emilyanthony4244/Sheikah_Slate/Assets/FB_IMG_1660274705326.jpg

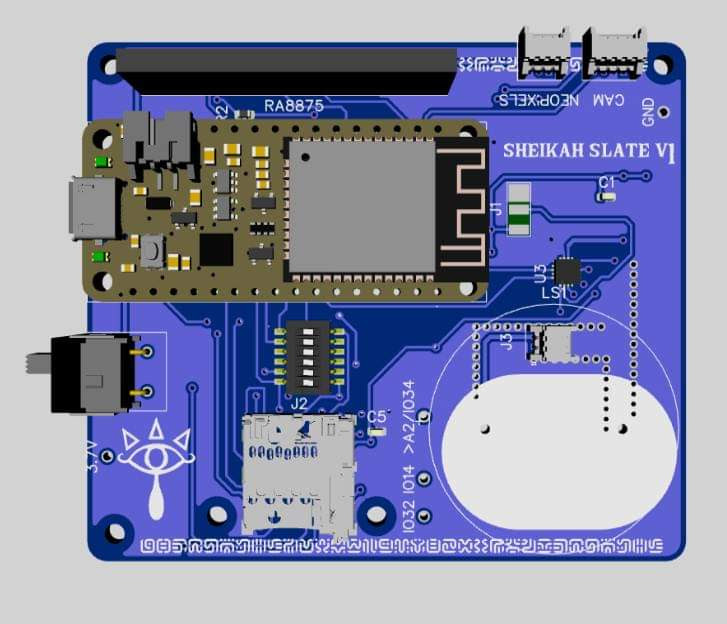
Assets/FB_IMG_1660274705326.jpg
