emilyanthony4244/Sheikah_Slate/Main Control Board/Bottom Copper.PNG

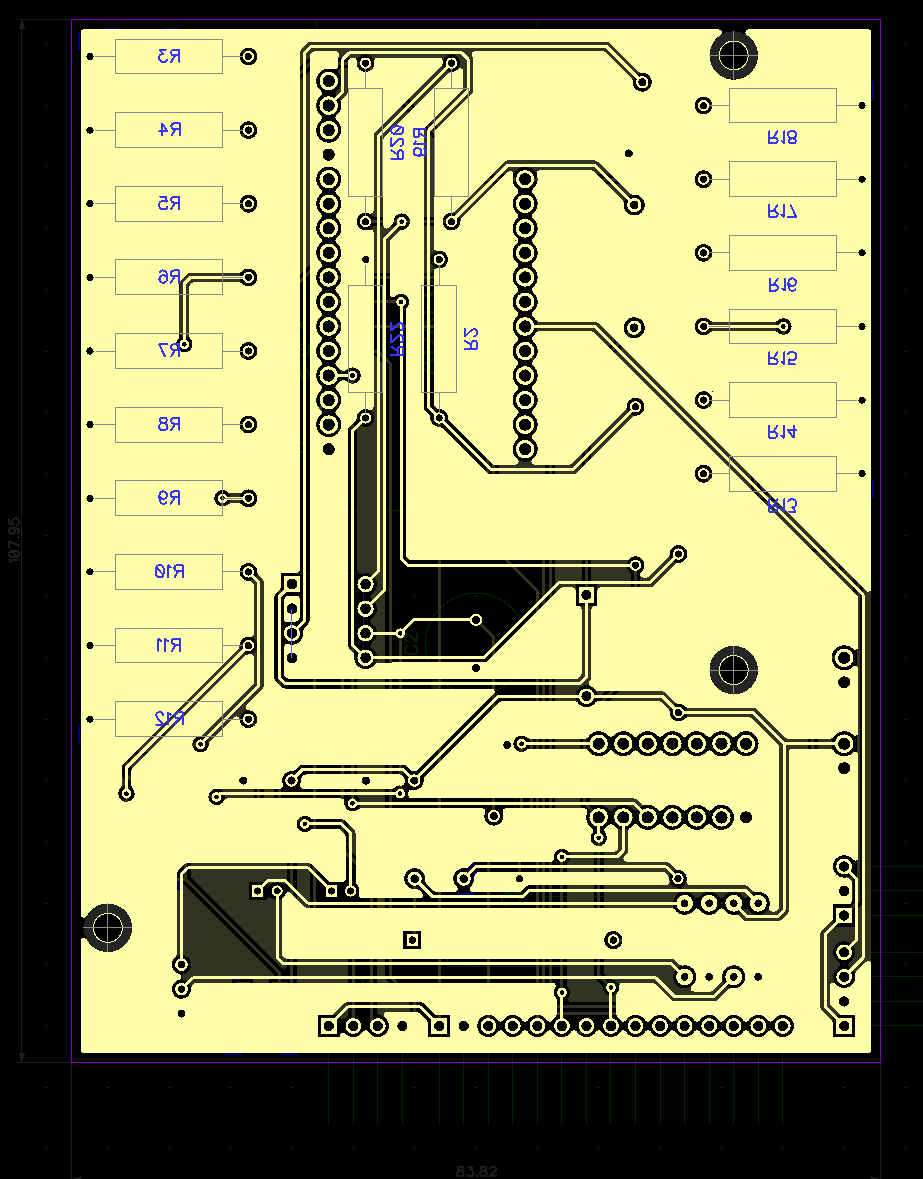
Main Control Board/Bottom Copper.PNG
