emilyanthony4244/Sheikah_Slate/Main Control Board/bottom.PNG

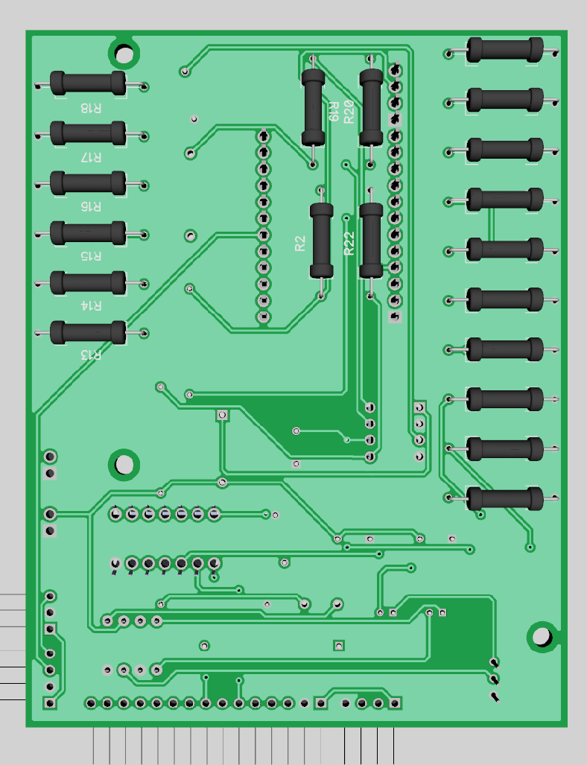
Main Control Board/bottom.PNG
