emilyanthony4244/Sheikah_Slate/Main Control Board/Top Copper.PNG

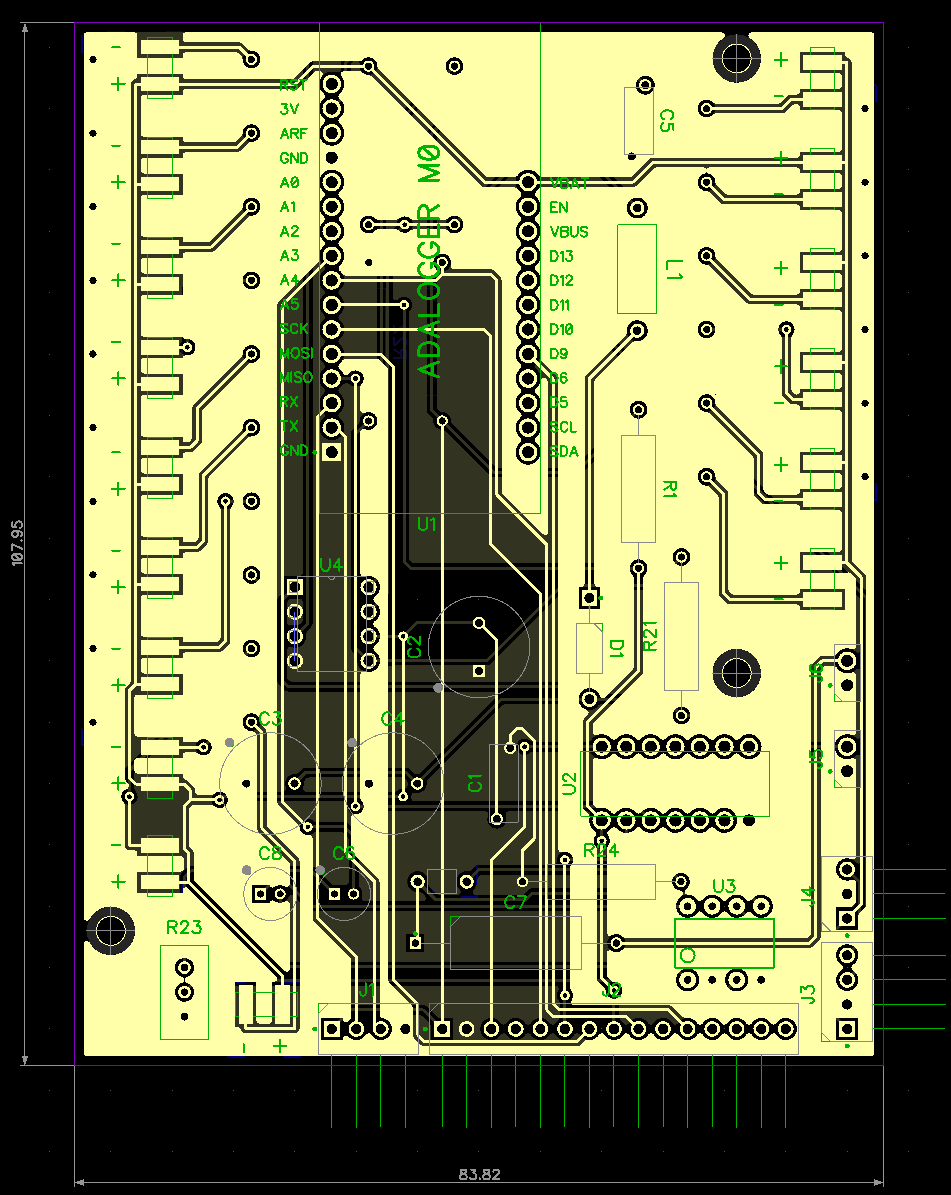
Main Control Board/Top Copper.PNG
