emilyanthony4244/Sheikah_Slate/Main Control Board/top.PNG

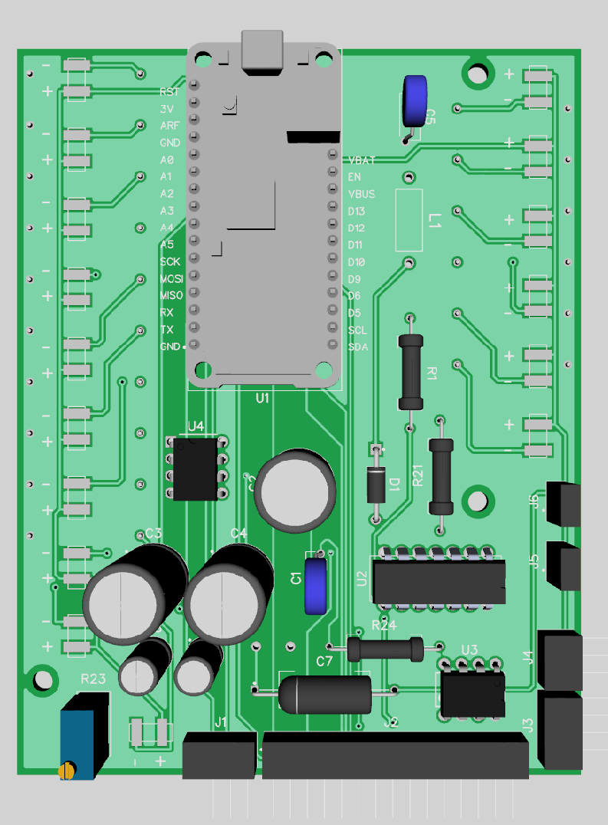
Main Control Board/top.PNG
