emilyanthony4244/Sheikah_Slate/SOLIDWORKS/sheikah slate/SLR-343DC3F.SLDPRT

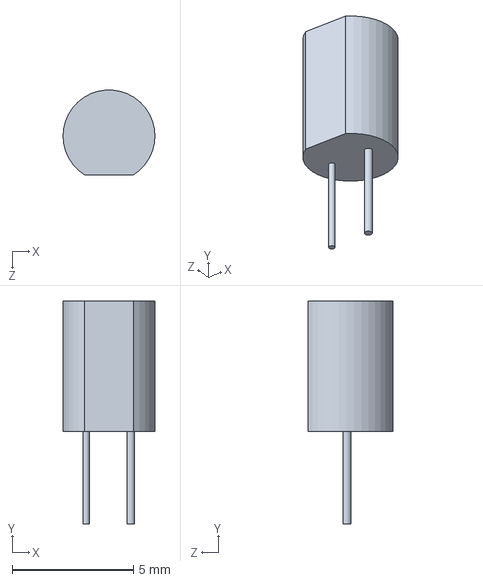
[picture p33: CAD file, 2022-02-20]
SOLIDWORKS/sheikah slate/SLR-343DC3F.SLDPRT
3.80 x 9.21 x 3.50 mm
