emilyanthony4244/Sheikah_Slate/SOLIDWORKS/Eyelash Orange LED1.SLDPRT

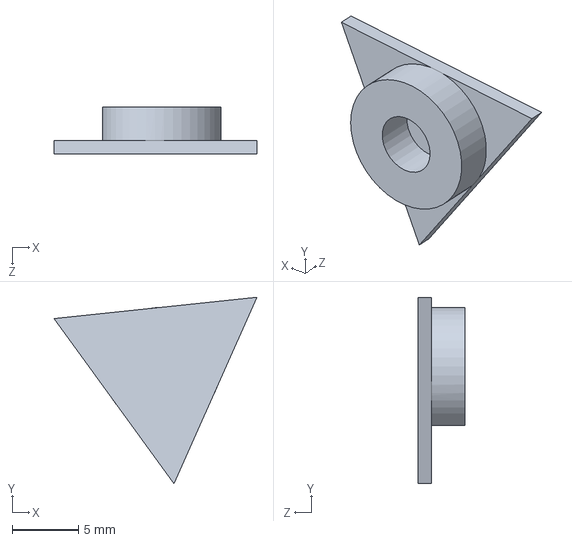
[picture p34: CAD file, 2022-02-20]
SOLIDWORKS/Eyelash Orange LED1.SLDPRT
15.3 x 14.1 x 3.54 mm
