emilyanthony4244/Sheikah_Slate/SOLIDWORKS/rocker switch 1.SLDPRT

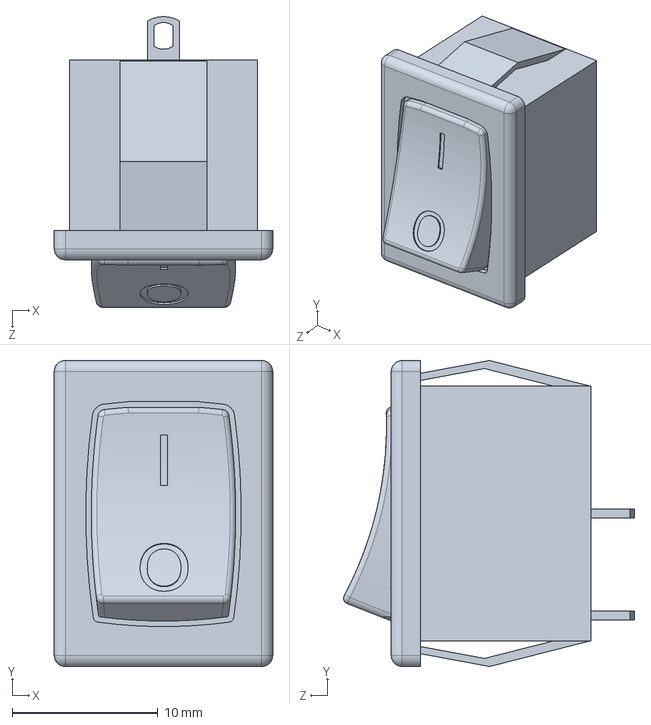
[picture p35: CAD file, 2022-02-20]
SOLIDWORKS/rocker switch 1.SLDPRT
15.0 x 21.0 x 20.0 mm
