emilyanthony4244/Sheikah_Slate/SOLIDWORKS/adafruit TTL mini camera.SLDPRT

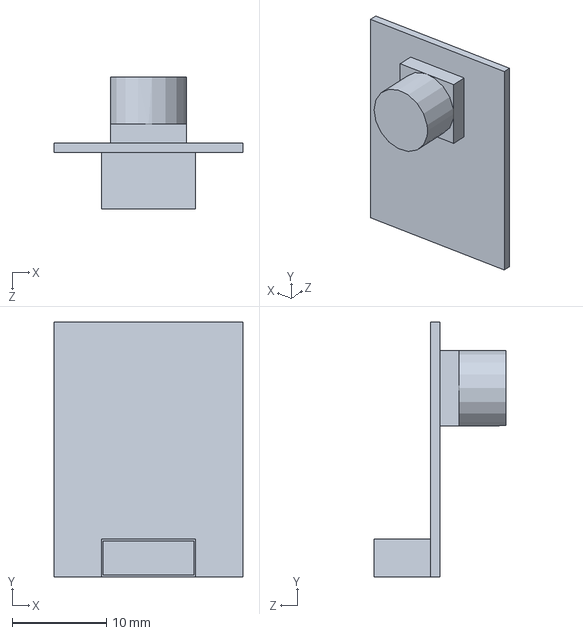
[picture p36: CAD file, 2022-02-20]
SOLIDWORKS/adafruit TTL mini camera.SLDPRT
20.0 x 27.0 x 14.0 mm
