emilyanthony4244/Sheikah_Slate/CAD/NeoPixel Mini Button PCB.SLDPRT

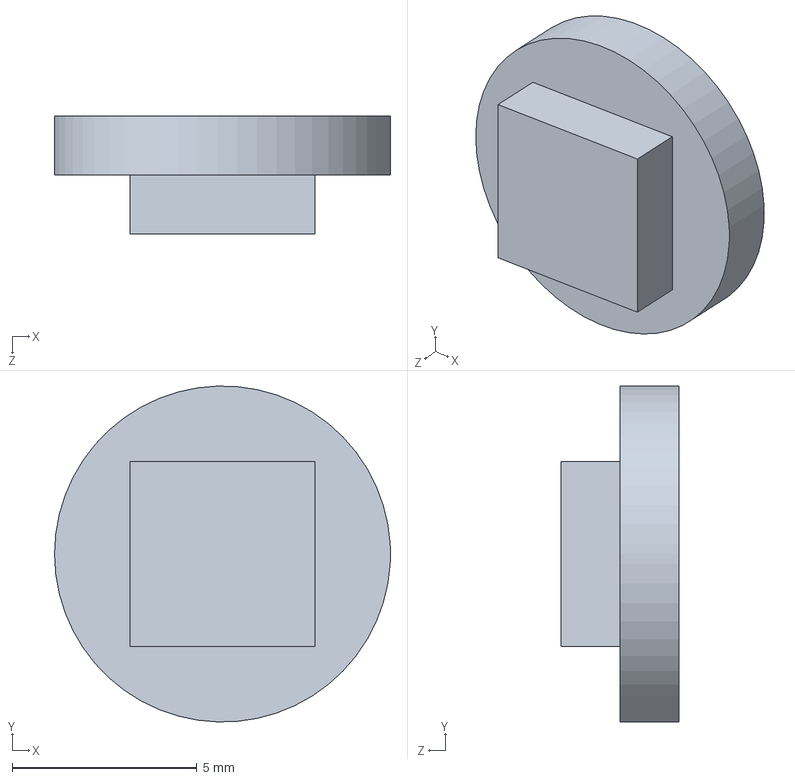
[picture p37: CAD file, 2023-08-10]
CAD/NeoPixel Mini Button PCB.SLDPRT
9.10 x 9.10 x 3.20 mm
