emilyanthony4244/Sheikah_Slate/CAD/Sheikah Slate Body Bottom.STL

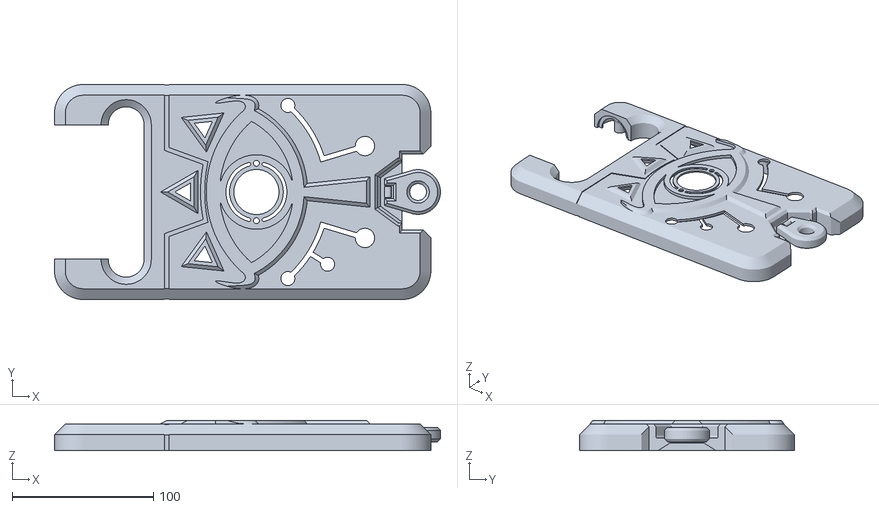
[picture p38: CAD file, 2023-08-10]
CAD/Sheikah Slate Body Bottom.STL
273.5 x 152.4 x 21.6
