emilyanthony4244/Sheikah_Slate/CAD/board_bare.step

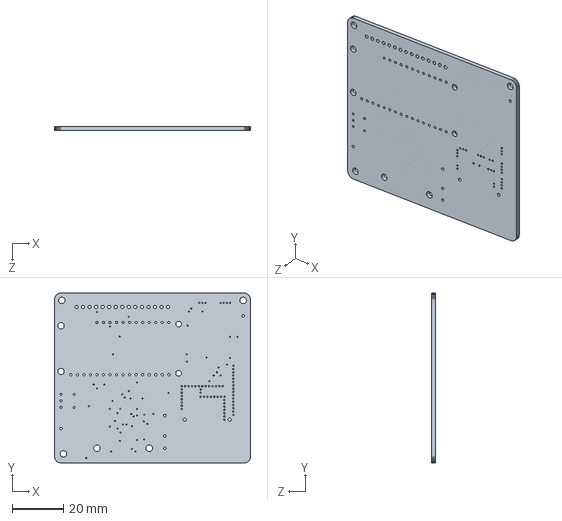
[picture p39: CAD file, 2023-08-10]
CAD/board_bare.step
76.2 x 66.0 x 1.59 mm
