emilyanthony4244/Sheikah_Slate/CAD/Sheikah Slate Body Bottom usb access.STL

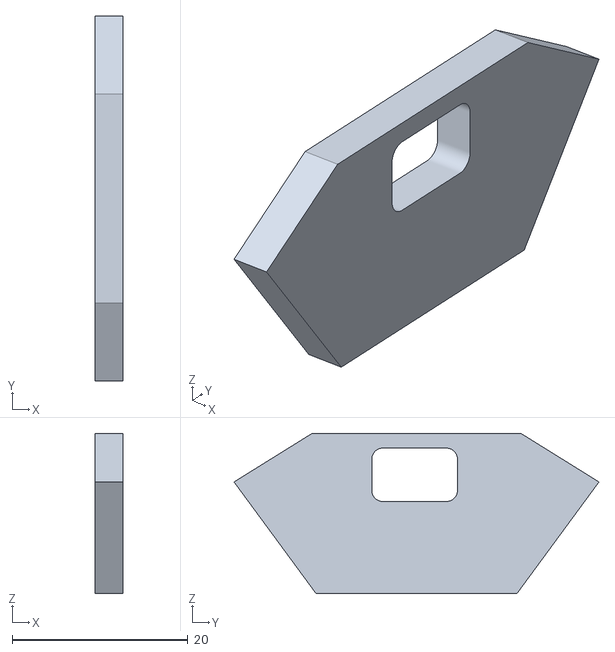
[picture p40: CAD file, 2023-08-10]
CAD/Sheikah Slate Body Bottom usb access.STL
3.18 x 41.5 x 18.2
