emilyanthony4244/Sheikah_Slate/SOLIDWORKS/Back Body.SLDPRT

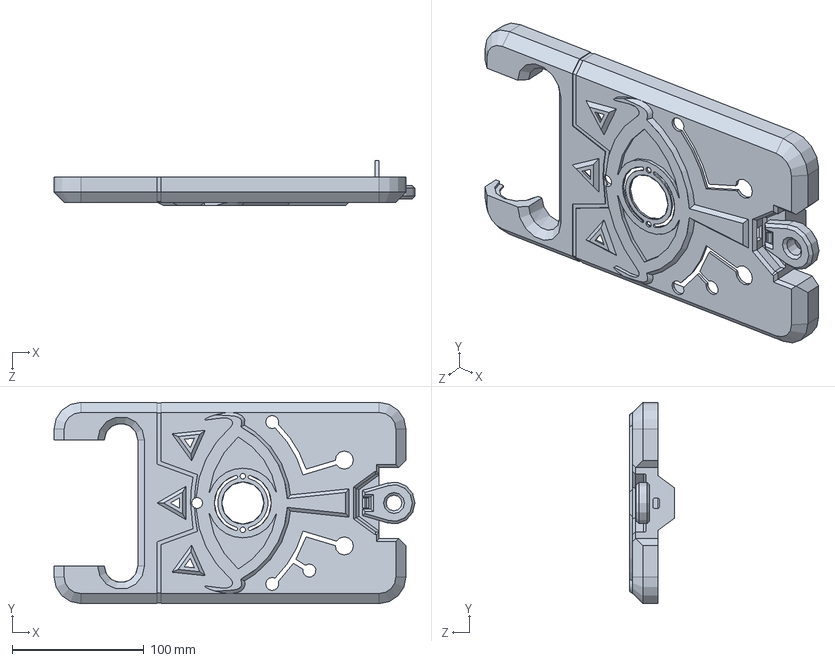
[picture p41: CAD file, 2022-02-20]
SOLIDWORKS/Back Body.SLDPRT
273.5 x 152.4 x 34.3 mm
