emilyanthony4244/Sheikah_Slate/SOLIDWORKS/NTE 54-872.SLDPRT

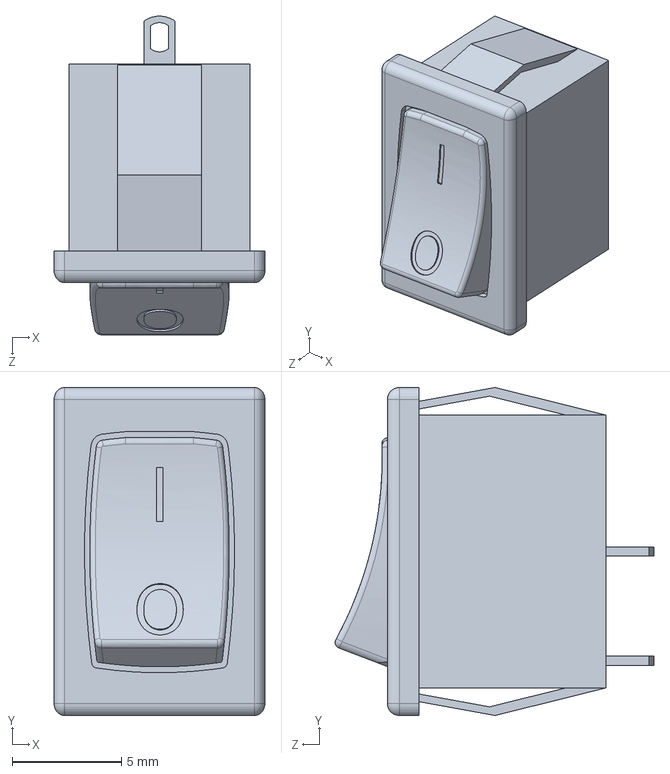
[picture p42: CAD file, 2022-02-20]
SOLIDWORKS/NTE 54-872.SLDPRT
9.65 x 15.0 x 14.6 mm
