emilyanthony4244/Sheikah_Slate/Arduino/main/camera.ino

void takepic(){
   Serial.println("Snap in 1 secs...");
  delay(1000);

  if (! cam.takePicture()) 
    Serial.println("Failed to snap!");
  else 
    Serial.println("Picture taken!");
  
  // TODO: come up with file name and folder structure;
  char filename[13];  //TODO adjust length here if image file name changes
  strcpy(filename, "IMAGE00.JPG");
  for (int i = 0; i < 100; i++) {
    filename[5] = '0' + i/10;
    filename[6] = '0' + i%10;
    // create if does not exist, do not open existing, write, sync after write
    if (! SD.exists(filename)) {
      break;
    }
  }
  
  // Open the file for writing
  File imgFile = SD.open(filename, FILE_WRITE);

  // Get the size of the image (frame) taken  
  uint16_t jpglen = cam.frameLength();
  Serial.print("Storing ");
  Serial.print(jpglen, DEC);
  Serial.print(" byte image.");

  int32_t time = millis();
  pinMode(8, OUTPUT);
  // Read all the data up to # bytes!
  byte wCount = 0; // For counting # of writes
  while (jpglen > 0) {
    // read 32 bytes at a time;
    uint8_t *buffer;
    uint8_t bytesToRead = min((uint16_t)32, jpglen); // change 32 to 64 for a speedup but may not work with all setups!
    buffer = cam.readPicture(bytesToRead);
    imgFile.write(buffer, bytesToRead);
    if(++wCount >= 64) { // Every 2K, give a little feedback so it doesn't appear locked up
      Serial.print('.');
      wCount = 0;
    }
    //Serial.print("Read ");  Serial.print(bytesToRead, DEC); Serial.println(" bytes");
    jpglen -= bytesToRead;
  }
  imgFile.close();

  time = millis() - time;
  Serial.println("done!");
  Serial.print(time); Serial.println(" ms elapsed");
}
